fablabnbg/RFID_CardReader/Software_ESP/20180328_220426.jpg

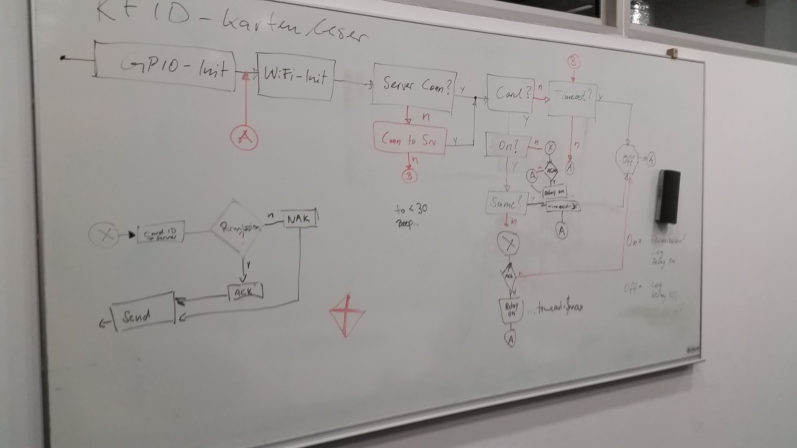
Software_ESP/20180328_220426.jpg
